huhu6608/Si4735_Radio/Simulation/Xtal_fliter.asc

C1: cap; 100n
C2: cap; 100n
C3: cap; 10n
C4: cap; 100n
C6: cap; 100n
C9: cap; 100n
L1: ind; 470µ
L2: ind; 470µ
R1: res; 800
R2: res; 470
R3: res; 50
R4: res; 800
R5: res; 14
R: res; 50
V1: voltage; PULSE(0 3.3 0 0.1p 0.1p 0.0000152587890625 30.517578125u)
Named nets: 0
.tran 0.5m
